bsamson/WFTF-Target-Checker/Solidworks/Parts/Cylinder.SLDPRT

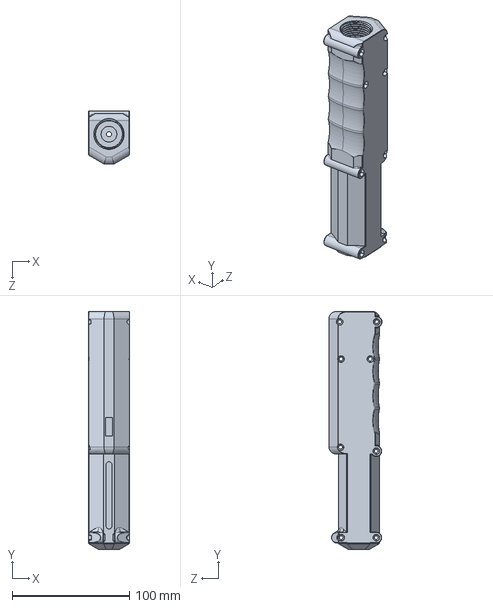
[picture p15: CAD file, 2015-11-04]
Solidworks/Parts/Cylinder.SLDPRT
35.0 x 203.0 x 45.3 mm
